simon-frankau/dirac/schematics/z80-schematics.kicad_sch

## KiCad design schematics/z80-schematics.kicad_sch (2023-09-10)

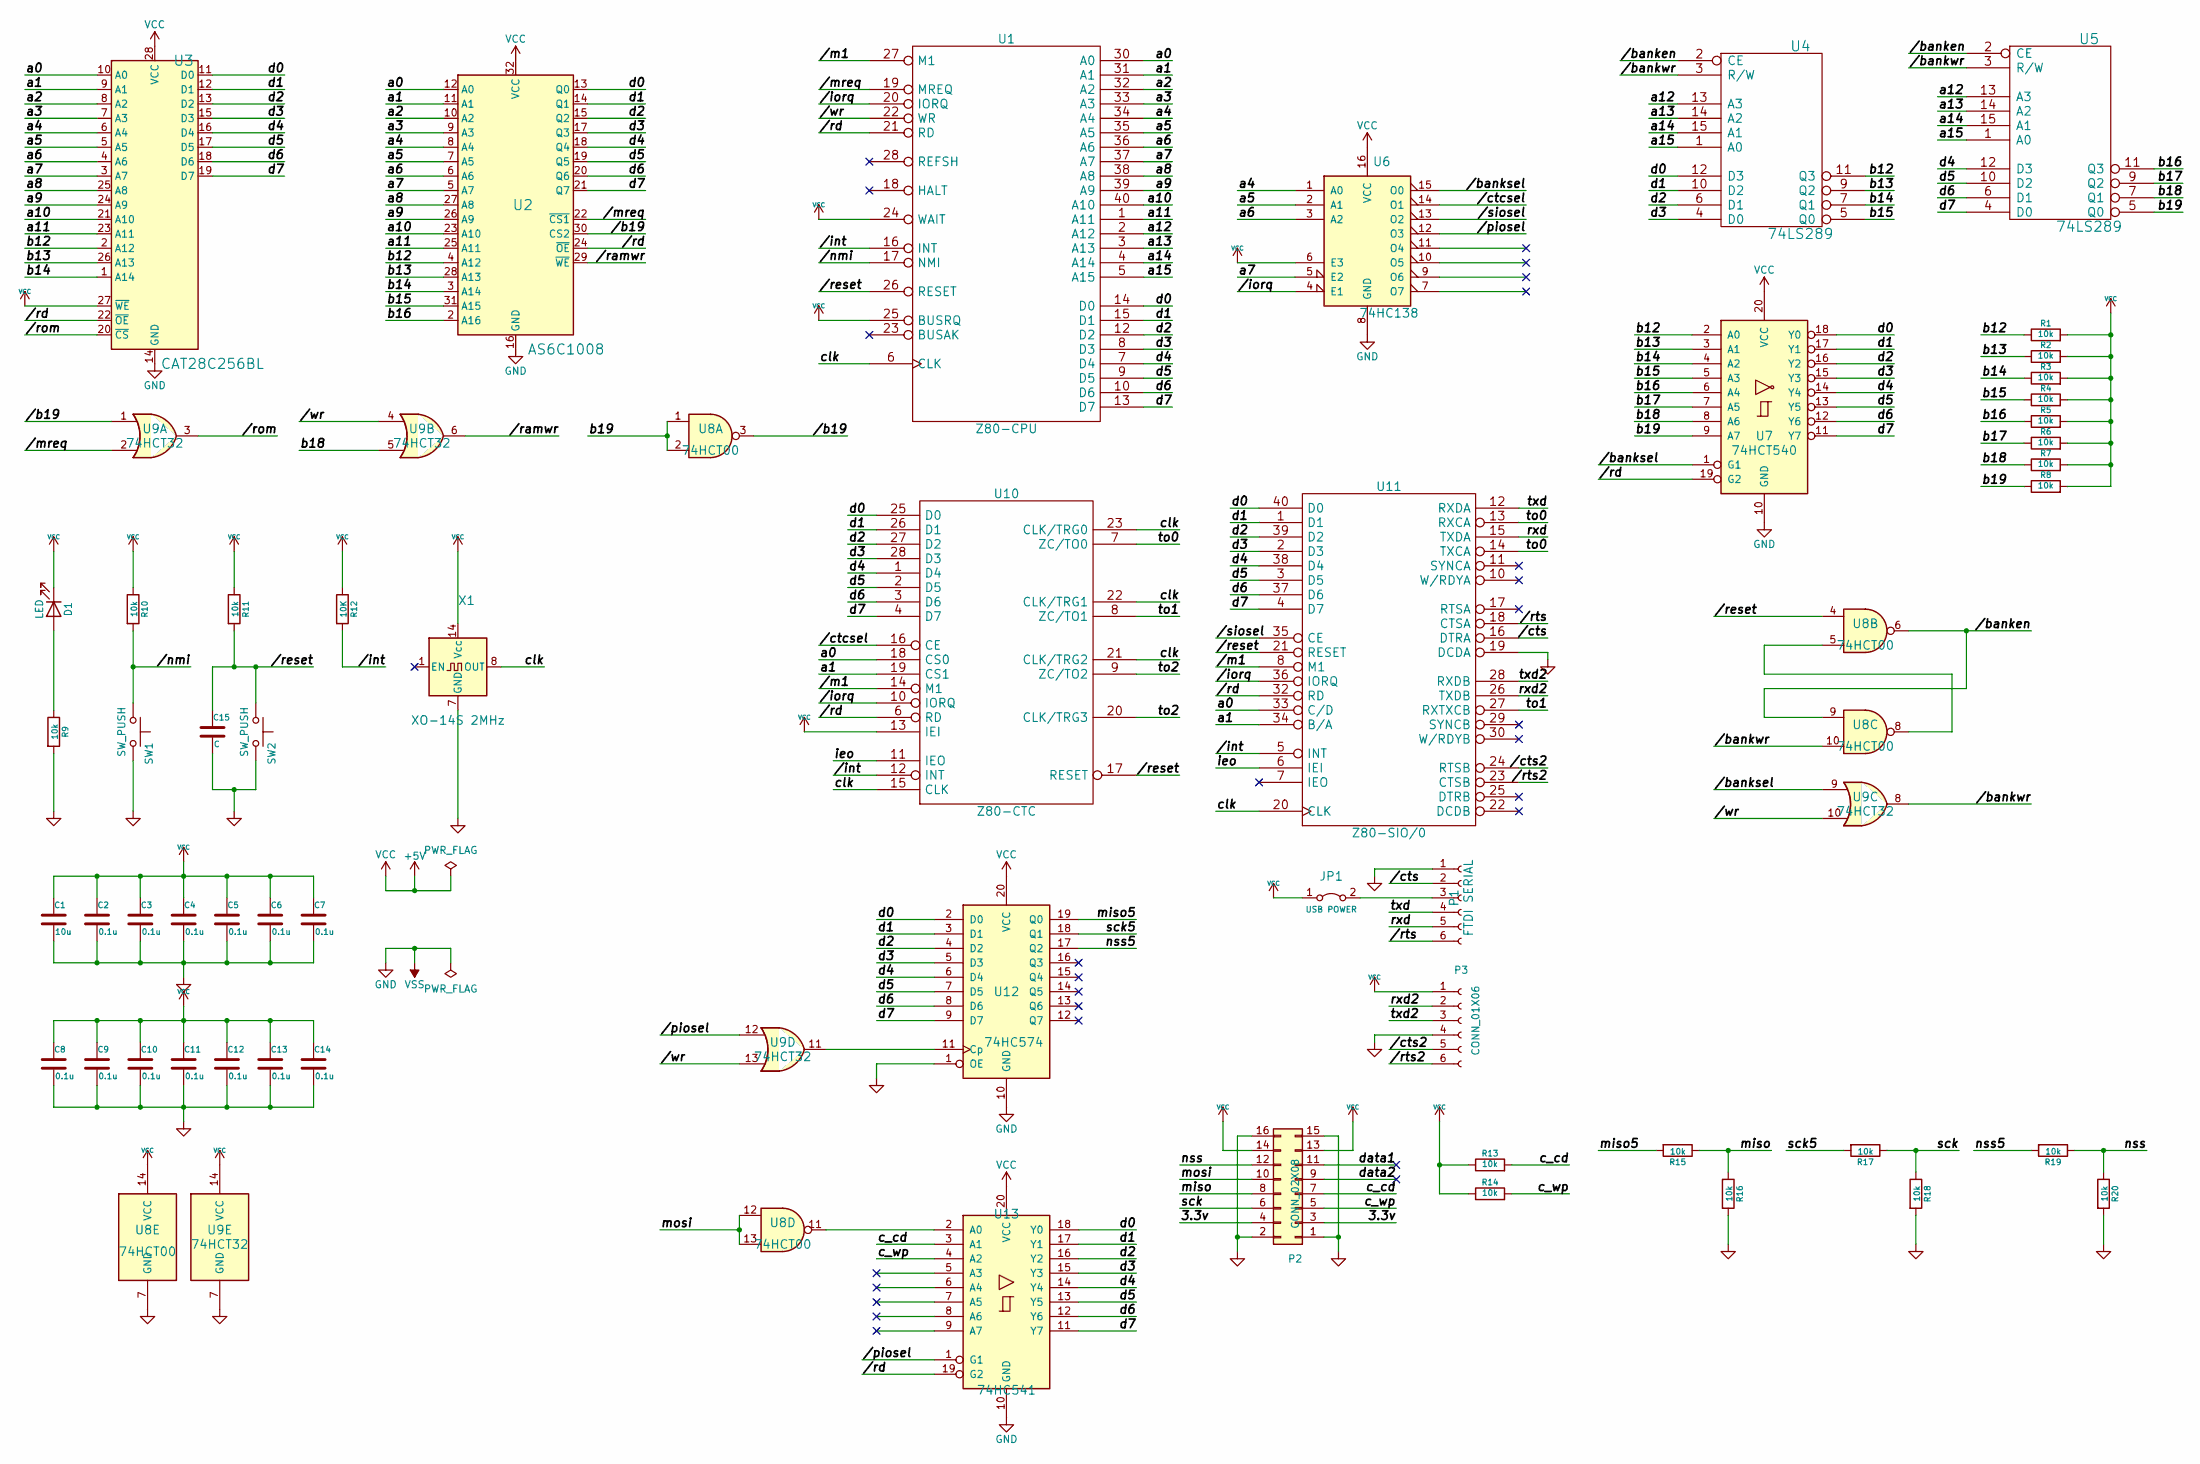
[picture p3: schematic z80-schematics.kicad_sch]

Parts:
C1: 10u
C2, C3, C4, C5, C6, C7, C8, C9, C10, C11, C12, C13, C14: 0.1u
C15: C
D1: LED
JP1: USB POWER
P1: FTDI SERIAL
P2: CONN_02X08
P3: CONN_01X06
R1, R2, R3, R4, R5, R6, R7, R8, R13, R14, R15, R16, R17, R18, R19, R20: 10k
R9, R10, R11: 10k
R12: 10K
SW1, SW2: SW_PUSH
U1: Z80-CPU
U2: AS6C1008
U3: CAT28C256BL
U4, U5: 74LS289
U6: 74HC138
U7: 74HCT540
U8: 74HCT00
U9: 74HCT32
U10: Z80-CTC
U11: Z80-SIO/0
U12: 74HC574
U13: 74HC541
X1: XO-14S 2MHz; Oscillator_DIP-14

Connections:
3.3v: P2.3, P2.4
+5V: C1.1, C2.1, C3.1, C4.1, C5.1, C6.1, C7.1, C8.1, C9.1, C10.1, C11.1, C12.1, C13.1, C14.1, D1.1 (K), JP1.1 (A), P2.13, P2.14, P3.1, R1.2, R2.2, R3.2, R4.2, R5.2, R6.2, R7.2, R8.2, R10.1, R11.1, R12.1, R13.1, R14.1, U1.24 (WAIT), U1.25 (BUSRQ), U2.32 (VCC), U3.27 (~WE), U3.28 (VCC), U6.6 (E3), U6.16 (VCC), U7.20 (VCC), U8.14 (VCC), U9.14 (VCC), U10.13 (IEI), U12.20 (VCC), U13.20 (VCC), X1.14 (Vcc)
/b19: U2.30 (CS2), U8.3, U9.1
/banken: U4.2 (CE), U5.2 (CE), U8.6, U8.9
/banksel: U6.15 (O0), U7.1 (G1), U9.9
/bankwr: U4.3 (R/W), U5.3 (R/W), U8.10, U9.8
/ctcsel: U6.14 (O1), U10.16 (CE)
/cts: P1.2, U11.16 (DTRA)
/cts2: P3.5, U11.24 (RTSB)
/int: R12.2, U1.16 (INT), U10.12 (INT), U11.5 (INT)
/iorq: U1.20 (IORQ), U6.4 (E1), U10.10 (IORQ), U11.36 (IORQ)
/m1: U1.27 (M1), U10.14 (M1), U11.8 (M1)
/mreq: U1.19 (MREQ), U2.22 (~CS1), U9.2
/nmi: R10.2, SW1.1, U1.17 (NMI)
/piosel: U6.12 (O3), U9.12, U13.1 (G1)
/ramwr: U2.29 (~WE), U9.6
/rd: U1.21 (RD), U2.24 (~OE), U3.22 (~OE), U7.19 (G2), U10.6 (RD), U11.32 (RD), U13.19 (G2)
/reset: C15.1, R11.2, SW2.1, U1.26 (RESET), U8.4, U10.17 (RESET), U11.21 (RESET)
/rom: U3.20 (~CS), U9.3
/rts: P1.6, U11.18 (CTSA)
/rts2: P3.6, U11.23 (CTSB)
/siosel: U6.13 (O2), U11.35 (CE)
/wr: U1.22 (WR), U9.4, U9.10, U9.13
GND: C1.2, C2.2, C3.2, C4.2, C5.2, C6.2, C7.2, C8.2, C9.2, C10.2, C11.2, C12.2, C13.2, C14.2, C15.2, P1.1, P2.1, P2.2, P2.15, P2.16, P3.4, R9.2, R16.2, R18.2, R20.2, SW1.2, SW2.2, U2.16 (GND), U3.14 (GND), U6.8 (GND), U7.10 (GND), U8.7 (GND), U9.7 (GND), U11.19 (DCDA), U12.1 (OE), U12.10 (GND), U13.10 (GND), X1.7 (GND)
unnamed: D1.2 (A), R9.1
unnamed: JP1.2 (B), P1.3
unnamed: U8.5, U8.8
unnamed: U9.11, U12.11 (Cp)
unnamed: U8.11, U13.2 (A0)
a0: U1.30 (A0), U2.12 (A0), U3.10 (A0), U10.18 (CS0), U11.33 (C/D)
a1: U1.31 (A1), U2.11 (A1), U3.9 (A1), U10.19 (CS1), U11.34 (B/A)
a2: U1.32 (A2), U2.10 (A2), U3.8 (A2)
a3: U1.33 (A3), U2.9 (A3), U3.7 (A3)
a4: U1.34 (A4), U2.8 (A4), U3.6 (A4), U6.1 (A0)
a5: U1.35 (A5), U2.7 (A5), U3.5 (A5), U6.2 (A1)
a6: U1.36 (A6), U2.6 (A6), U3.4 (A6), U6.3 (A2)
a7: U1.37 (A7), U2.5 (A7), U3.3 (A7), U6.5 (E2)
a8: U1.38 (A8), U2.27 (A8), U3.25 (A8)
a9: U1.39 (A9), U2.26 (A9), U3.24 (A9)
a10: U1.40 (A10), U2.23 (A10), U3.21 (A10)
a11: U1.1 (A11), U2.25 (A11), U3.23 (A11)
a12: U1.2 (A12), U4.13 (A3), U5.13 (A3)
a13: U1.3 (A13), U4.14 (A2), U5.14 (A2)
a14: U1.4 (A14), U4.15 (A1), U5.15 (A1)
a15: U1.5 (A15), U4.1 (A0), U5.1 (A0)
b12: R1.1, U2.4 (A12), U3.2 (A12), U4.11 (Q3), U7.2 (A0)
b13: R2.1, U2.28 (A13), U3.26 (A13), U4.9 (Q2), U7.3 (A1)
b14: R3.1, U2.3 (A14), U3.1 (A14), U4.7 (Q1), U7.4 (A2)
b15: R4.1, U2.31 (A15), U4.5 (Q0), U7.5 (A3)
b16: R5.1, U2.2 (A16), U5.11 (Q3), U7.6 (A4)
b17: R6.1, U5.9 (Q2), U7.7 (A5)
b18: R7.1, U5.7 (Q1), U7.8 (A6), U9.5
b19: R8.1, U5.5 (Q0), U7.9 (A7), U8.1, U8.2
c_cd: P2.7, R13.2, U13.3 (A1)
c_wp: P2.5, R14.2, U13.4 (A2)
clk: U1.6 (CLK), U10.15 (CLK), U10.21 (CLK/TRG2), U10.22 (CLK/TRG1), U10.23 (CLK/TRG0), U11.20 (CLK), X1.8 (OUT)
d0: U1.14 (D0), U2.13 (Q0), U3.11 (D0), U4.12 (D3), U7.18 (Y0), U10.25 (D0), U11.40 (D0), U12.2 (D0), U13.18 (Y0)
d1: U1.15 (D1), U2.14 (Q1), U3.12 (D1), U4.10 (D2), U7.17 (Y1), U10.26 (D1), U11.1 (D1), U12.3 (D1), U13.17 (Y1)
d2: U1.12 (D2), U2.15 (Q2), U3.13 (D2), U4.6 (D1), U7.16 (Y2), U10.27 (D2), U11.39 (D2), U12.4 (D2), U13.16 (Y2)
d3: U1.8 (D3), U2.17 (Q3), U3.15 (D3), U4.4 (D0), U7.15 (Y3), U10.28 (D3), U11.2 (D3), U12.5 (D3), U13.15 (Y3)
d4: U1.7 (D4), U2.18 (Q4), U3.16 (D4), U5.12 (D3), U7.14 (Y4), U10.1 (D4), U11.38 (D4), U12.6 (D4), U13.14 (Y4)
d5: U1.9 (D5), U2.19 (Q5), U3.17 (D5), U5.10 (D2), U7.13 (Y5), U10.2 (D5), U11.3 (D5), U12.7 (D5), U13.13 (Y5)
d6: U1.10 (D6), U2.20 (Q6), U3.18 (D6), U5.6 (D1), U7.12 (Y6), U10.3 (D6), U11.37 (D6), U12.8 (D6), U13.12 (Y6)
d7: U1.13 (D7), U2.21 (Q7), U3.19 (D7), U5.4 (D0), U7.11 (Y7), U10.4 (D7), U11.4 (D7), U12.9 (D7), U13.11 (Y7)
data1: P2.11
data2: P2.9
ieo: U10.11 (IEO), U11.6 (IEI)
miso: P2.8, R15.1, R16.1
miso5: R15.2, U12.19 (Q0)
mosi: P2.10, U8.12, U8.13
nss: P2.12, R19.1, R20.1
nss5: R19.2, U12.17 (Q2)
rxd: P1.5, U11.15 (TXDA)
rxd2: P3.2, U11.26 (TXDB)
sck: P2.6, R17.1, R18.1
sck5: R17.2, U12.18 (Q1)
to0: U10.7 (ZC/TO0), U11.13 (RXCA), U11.14 (TXCA)
to1: U10.8 (ZC/TO1), U11.27 (RXTXCB)
to2: U10.9 (ZC/TO2), U10.20 (CLK/TRG3)
txd: P1.4, U11.12 (RXDA)
txd2: P3.3, U11.28 (RXDB)
