simon-frankau/dirac/schematics/sdcard/sdcard.kicad_sch

## KiCad design schematics/sdcard/sdcard.kicad_sch (2023-09-10)

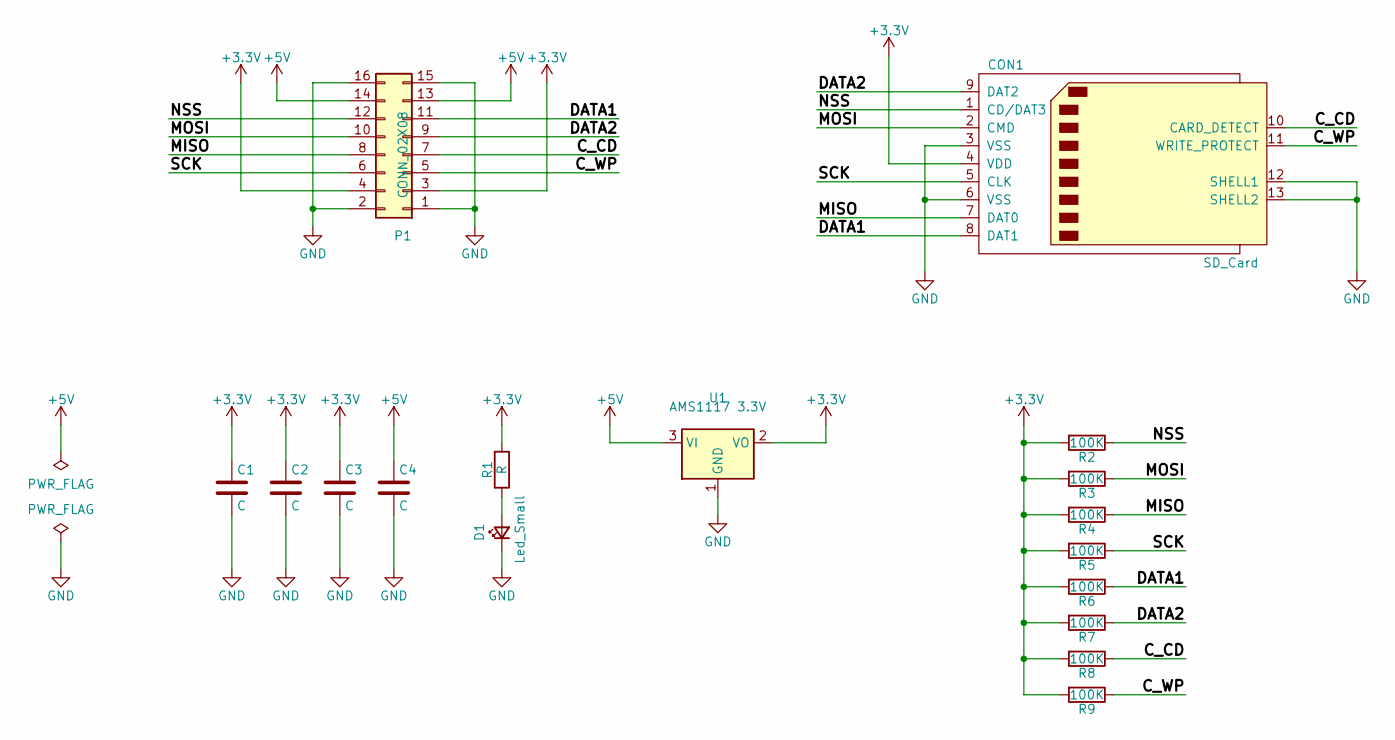
[picture p4: schematic sdcard.kicad_sch]

Parts:
C1, C2, C3, C4: C
CON1: SD_Card; 10067847-001
D1: Led_Small
P1: CONN_02X08
R1: R
R2, R3, R4, R5, R6, R7, R8, R9: 100K
U1: AMS1117 3.3V; SOT-223-3_TabPin2

Connections:
+3.3V: C1.1, C2.1, C3.1, CON1.4 (VDD), P1.3, P1.4, R1.2, R2.2, R3.2, R4.2, R5.2, R6.2, R7.2, R8.2, R9.2, U1.2 (VO)
+5V: C4.1, P1.13, P1.14, U1.3 (VI)
C_CD: CON1.10 (CARD_DETECT), P1.7, R8.1
C_WP: CON1.11 (WRITE_PROTECT), P1.5, R9.1
DATA1: CON1.8 (DAT1), P1.11, R6.1
DATA2: CON1.9 (DAT2), P1.9, R7.1
GND: C1.2, C2.2, C3.2, C4.2, CON1.3 (VSS), CON1.6 (VSS), CON1.12 (SHELL1), CON1.13 (SHELL2), D1.1 (K), P1.1, P1.2, P1.15, P1.16, U1.1 (GND)
MISO: CON1.7 (DAT0), P1.8, R4.1
MOSI: CON1.2 (CMD), P1.10, R3.1
NSS: CON1.1 (CD/DAT3), P1.12, R2.1
unnamed: D1.2 (A), R1.1
SCK: CON1.5 (CLK), P1.6, R5.1
